ERDALECE/ZeyBack/Pictures/res3.jpg

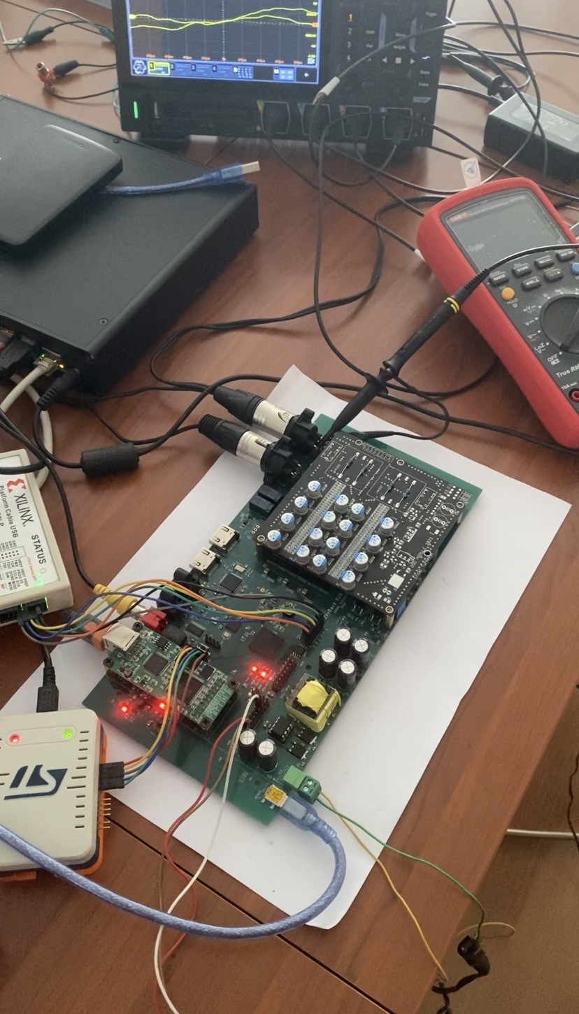
Pictures/res3.jpg
