ERDALECE/ZeyBack/Pictures/res7.jpg

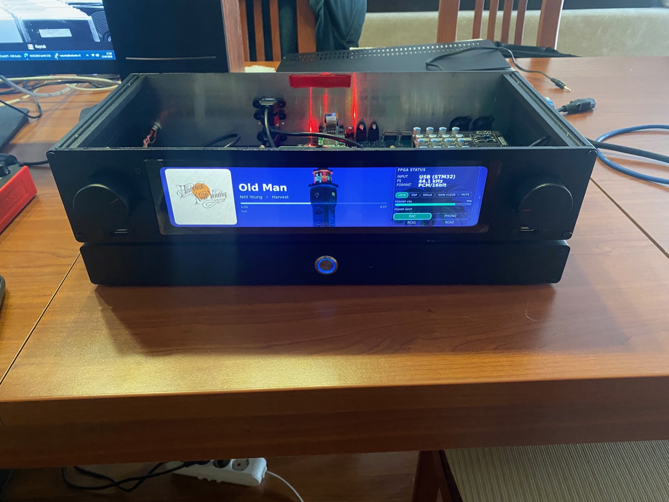
Pictures/res7.jpg
