ERDALECE/ZeyBack/Firmware/Stm32/Core/Inc/192khz.h

#ifndef _192KHZ_BIN_H
#define _192KHZ_BIN_H

static const unsigned char _192khz_bin[] = {
		0x00, 0xff, 0xff, 0xff, 0xff, 0xff, 0xff, 0x00, 0x05, 0xd7, 0x00, 0x00,
		0x00, 0x00, 0x00, 0x00, 0xff, 0x23, 0x01, 0x03, 0x80, 0x32, 0x1f, 0x78,
		0x07, 0xee, 0x95, 0xa3, 0x54, 0x4c, 0x99, 0x26, 0x0f, 0x50, 0x54, 0x00,
		0x00, 0x00, 0x01, 0x01, 0x01, 0x01, 0x01, 0x01, 0x01, 0x01, 0x01, 0x01,
		0x01, 0x01, 0x01, 0x01, 0x01, 0x01, 0x29, 0x36, 0x80, 0xa0, 0x70, 0x38,
		0x1f, 0x40, 0x30, 0x20, 0x35, 0x00, 0x63, 0xc8, 0x10, 0x00, 0x00, 0x1a,
		0x00, 0x00, 0x00, 0xfd, 0x00, 0x17, 0xf0, 0x0f, 0xff, 0x0e, 0x00, 0x0a,
		0x20, 0x20, 0x20, 0x20, 0x20, 0x20, 0x00, 0x00, 0x00, 0xfc, 0x00, 0x31,
		0x39, 0x32, 0x30, 0x78, 0x31, 0x30, 0x38, 0x30, 0x20, 0x43, 0x56, 0x54,
		0x00, 0x00, 0x00, 0x00, 0x00, 0x00, 0x00, 0x00, 0x00, 0x00, 0x00, 0x00,
		0x00, 0x00, 0x00, 0x00, 0x00, 0x00, 0x01, 0x0b, 0x02, 0x03, 0x18, 0x40,
		0x23, 0x09, 0x7e, 0x07, 0x67, 0x03, 0x0c, 0x00, 0x00, 0x00, 0x10, 0x1c,
		0x67, 0xd8, 0x5d, 0xc4, 0x01, 0x1c, 0x80, 0x00, 0x00, 0x00, 0x00, 0x00,
		0x00, 0x00, 0x00, 0x00, 0x00, 0x00, 0x00, 0x00, 0x00, 0x00, 0x00, 0x00,
		0x00, 0x00, 0x00, 0x00, 0x00, 0x00, 0x00, 0x00, 0x00, 0x00, 0x00, 0x00,
		0x00, 0x00, 0x00, 0x00, 0x00, 0x00, 0x00, 0x00, 0x00, 0x00, 0x00, 0x00,
		0x00, 0x00, 0x00, 0x00, 0x00, 0x00, 0x00, 0x00, 0x00, 0x00, 0x00, 0x00,
		0x00, 0x00, 0x00, 0x00, 0x00, 0x00, 0x00, 0x00, 0x00, 0x00, 0x00, 0x00,
		0x00, 0x00, 0x00, 0x00, 0x00, 0x00, 0x00, 0x00, 0x00, 0x00, 0x00, 0x00,
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

  // Filler / reserved (till byte 255)
  0x00, 0x00, 0x00, 0x00, 0x00, 0x00,
  0x00, 0x00, 0x00, 0x00, 0x00, 0x00,
  0x00, 0x00, 0x00, 0x00,

  // Checksum Block 1 (Byte 255)
  0xF9  // <-- Checksum byte for 2nd block: makes total sum % 256 == 0
};

unsigned char EDID_Buf[2][256] ;

/*
uint8_t TX_ADV7611_EDID0 [2] = {0x00, 0x00};
uint8_t TX_ADV7611_EDID1 [2] = {0x01, 0xff};
uint8_t TX_ADV7611_EDID2 [2] = {0x02, 0xff};
uint8_t TX_ADV7611_EDID3 [2] = {0x03, 0xff};
uint8_t TX_ADV7611_EDID4 [2] = {0x04, 0xff};
uint8_t TX_ADV7611_EDID5 [2] = {0x05, 0xff};
uint8_t TX_ADV7611_EDID6 [2] = {0x06, 0xff};
uint8_t TX_ADV7611_EDID7 [2] = {0x07, 0xff};
uint8_t TX_ADV7611_EDID8 [2] = {0x08, 0x00};
uint8_t TX_ADV7611_EDID9 [2] = {0x09, 0x05};
uint8_t TX_ADV7611_EDID10 [2] = {0x0A, 0xd7};
uint8_t TX_ADV7611_EDID11 [2] = {0x0B, 0x00};
uint8_t TX_ADV7611_EDID12 [2] = {0x0C, 0x00};
uint8_t TX_ADV7611_EDID13 [2] = {0x0D, 0x00};
uint8_t TX_ADV7611_EDID14 [2] = {0x0E, 0x00};
uint8_t TX_ADV7611_EDID15 [2] = {0x0F, 0x00};
uint8_t TX_ADV7611_EDID0 [2] = {0x10, 0xff};
uint8_t TX_ADV7611_EDID1 [2] = {0x11, 0x23};
uint8_t TX_ADV7611_EDID2 [2] = {0x12, 0x01};
uint8_t TX_ADV7611_EDID3 [2] = {0x13, 0x03};
uint8_t TX_ADV7611_EDID4 [2] = {0x44, 0x80};
uint8_t TX_ADV7611_EDID5 [2] = {0x15, 0x32};
uint8_t TX_ADV7611_EDID6 [2] = {0x16, 0x1f};
uint8_t TX_ADV7611_EDID7 [2] = {0x17, 0x78};
uint8_t TX_ADV7611_EDID8 [2] = {0x18, 0x07};
uint8_t TX_ADV7611_EDID9 [2] = {0x19, 0xee};
uint8_t TX_ADV7611_EDID10 [2] = {0x1A, 0x95};
uint8_t TX_ADV7611_EDID11 [2] = {0x1B, 0xa3};
uint8_t TX_ADV7611_EDID12 [2] = {0x1C, 0x54};
uint8_t TX_ADV7611_EDID13 [2] = {0x1D, 0x4c};
uint8_t TX_ADV7611_EDID14 [2] = {0x1E, 0x99};
uint8_t TX_ADV7611_EDID15 [2] = {0x1F, 0x26};
uint8_t TX_ADV7611_EDID0 [2] = {0x20, 0x0f};
uint8_t TX_ADV7611_EDID1 [2] = {0x21, 0x00};
uint8_t TX_ADV7611_EDID2 [2] = {0x22, 0x00};
uint8_t TX_ADV7611_EDID3 [2] = {0x23, 0x00};
uint8_t TX_ADV7611_EDID4 [2] = {0x24, 0x00};
uint8_t TX_ADV7611_EDID5 [2] = {0x25, 0x00};
uint8_t TX_ADV7611_EDID6 [2] = {0x26, 0x00};
uint8_t TX_ADV7611_EDID7 [2] = {0x27, 0x00};
uint8_t TX_ADV7611_EDID8 [2] = {0x28, 0x00};
uint8_t TX_ADV7611_EDID9 [2] = {0x29, 0x00};
uint8_t TX_ADV7611_EDID10 [2] = {0x2A, 0x00};
uint8_t TX_ADV7611_EDID11 [2] = {0x2B, 0x00};
uint8_t TX_ADV7611_EDID12 [2] = {0x2C, 0x00};
uint8_t TX_ADV7611_EDID13 [2] = {0x2D, 0x00};
uint8_t TX_ADV7611_EDID14 [2] = {0x2E, 0x00};
uint8_t TX_ADV7611_EDID15 [2] = {0x2F, 0x00};
*/

#endif /* _192KHZ_BIN_H */
