ERDALECE/ZeyBack/Firmware/Stm32/Core/Inc/SI5340_conf.h

/*
 * SI5340_conf.h
 *
 *  Created on: Jun 30, 2025
 *      Author: Erdalpc
 */

#ifndef INC_SI5340_CONF_H_
#define INC_SI5340_CONF_H_

/*
 * Si5340 Rev D Configuration Register Export Header File
 *
 * This file represents a series of Skyworks Si5340 Rev D
 * register writes that can be performed to load a single configuration
 * on a device. It was created by a Skyworks ClockBuilder Pro
 * export tool.
 *
 * Part:		                                       Si5340 Rev D
 * Design ID:                                          r2rdac
 * Includes Pre/Post Download Control Register Writes: Yes
 * Created By:                                         ClockBuilder Pro v4.15.0.2 [2025-05-07]
 * Timestamp:                                          2025-06-30 00:35:52 GMT+03:00
 *
 * A complete design report corresponding to this export is included at the end
 * of this header file.
 *
 */

si5340_revd_register_t const si5340_revd_registers_98_90[SI5340_REVD_REG_CONFIG_NUM_REGS] =
{

	/* Start configuration preamble */
	{ 0x0B24, 0xC0 },
	{ 0x0B25, 0x00 },
	/* Rev D stuck divider fix */
	{ 0x0502, 0x01 },
	{ 0x0505, 0x03 },
	{ 0x0957, 0x17 },
	{ 0x0B4E, 0x1A },
	/* End configuration preamble */

	/* Delay 300 msec */
	/*    Delay is worst case time for device to complete any calibration */
	/*    that is running due to device state change previous to this script */
	/*    being processed. */

	/* Start configuration registers */
	{ 0x0006, 0x00 },
	{ 0x0007, 0x00 },
	{ 0x0008, 0x00 },
	{ 0x000B, 0x74 },
	{ 0x0017, 0xD0 },
	{ 0x0018, 0xFE },
	{ 0x0021, 0x0F },
	{ 0x0022, 0x00 },
	{ 0x002B, 0x02 },
	{ 0x002C, 0x21 },
	{ 0x002D, 0x00 },
	{ 0x002E, 0x91 },
	{ 0x002F, 0x00 },
	{ 0x0030, 0x00 },
	{ 0x0031, 0x00 },
	{ 0x0032, 0x00 },
	{ 0x0033, 0x00 },
	{ 0x0034, 0x00 },
	{ 0x0035, 0x00 },
	{ 0x0036, 0x91 },
	{ 0x0037, 0x00 },
	{ 0x0038, 0x00 },
	{ 0x0039, 0x00 },
	{ 0x003A, 0x00 },
	{ 0x003B, 0x00 },
	{ 0x003C, 0x00 },
	{ 0x003D, 0x00 },
	{ 0x0041, 0x05 },
	{ 0x0042, 0x00 },
	{ 0x0043, 0x00 },
	{ 0x0044, 0x00 },
	{ 0x009E, 0x00 },
	{ 0x0102, 0x01 },
	{ 0x0112, 0x06 },
	{ 0x0113, 0xCC },
	{ 0x0114, 0x00 },
	{ 0x0115, 0x08 },
	{ 0x0117, 0x01 },
	{ 0x0118, 0x09 },
	{ 0x0119, 0x3B },
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
	/* End configuration registers */

	/* Start configuration postamble */
	{ 0x001C, 0x01 },
	{ 0x0B24, 0xC3 },
	{ 0x0B25, 0x02 },
	/* End configuration postamble */

};





si5340_revd_register_t const si5340_revd_registers_90[SI5340_REVD_REG_CONFIG_NUM_REGS] =
{

	/* Start configuration preamble */
	{ 0x0B24, 0xC0 },
	{ 0x0B25, 0x00 },
	/* Rev D stuck divider fix */
	{ 0x0502, 0x01 },
	{ 0x0505, 0x03 },
	{ 0x0957, 0x17 },
	{ 0x0B4E, 0x1A },
	/* End configuration preamble */

	/* Delay 300 msec */
	/*    Delay is worst case time for device to complete any calibration */
	/*    that is running due to device state change previous to this script */
	/*    being processed. */

	/* Start configuration registers */
	{ 0x0006, 0x00 },
	{ 0x0007, 0x00 },
	{ 0x0008, 0x00 },
	{ 0x000B, 0x74 },
	{ 0x0017, 0xD0 },
	{ 0x0018, 0xFE },
	{ 0x0021, 0x0F },
	{ 0x0022, 0x00 },
	{ 0x002B, 0x02 },
	{ 0x002C, 0x21 },
	{ 0x002D, 0x00 },
	{ 0x002E, 0x89 },
	{ 0x002F, 0x00 },
	{ 0x0030, 0x00 },
	{ 0x0031, 0x00 },
	{ 0x0032, 0x00 },
	{ 0x0033, 0x00 },
	{ 0x0034, 0x00 },
	{ 0x0035, 0x00 },
	{ 0x0036, 0x89 },
	{ 0x0037, 0x00 },
	{ 0x0038, 0x00 },
	{ 0x0039, 0x00 },
	{ 0x003A, 0x00 },
	{ 0x003B, 0x00 },
	{ 0x003C, 0x00 },
	{ 0x003D, 0x00 },
	{ 0x0041, 0x05 },
	{ 0x0042, 0x00 },
	{ 0x0043, 0x00 },
	{ 0x0044, 0x00 },
	{ 0x009E, 0x00 },
	{ 0x0102, 0x01 },
	{ 0x0112, 0x02 },
	{ 0x0113, 0xCC },
	{ 0x0114, 0x00 },
	{ 0x0115, 0x09 },
	{ 0x0117, 0x01 },
	{ 0x0118, 0x09 },
	{ 0x0119, 0x3B },
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
	/* End configuration registers */

	/* Start configuration postamble */
	{ 0x001C, 0x01 },
	{ 0x0B24, 0xC3 },
	{ 0x0B25, 0x02 },
	/* End configuration postamble */

};


si5340_revd_register_t const si5340_revd_registers_11[SI5340_REVD_REG_CONFIG_NUM_REGS] =
{

	/* Start configuration preamble */
	{ 0x0B24, 0xC0 },
	{ 0x0B25, 0x00 },
	/* Rev D stuck divider fix */
	{ 0x0502, 0x01 },
	{ 0x0505, 0x03 },
	{ 0x0957, 0x17 },
	{ 0x0B4E, 0x1A },
	/* End configuration preamble */

	/* Delay 300 msec */
	/*    Delay is worst case time for device to complete any calibration */
	/*    that is running due to device state change previous to this script */
	/*    being processed. */

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
	{ 0x0113, 0xCC },
	{ 0x0114, 0x00 },
	{ 0x0115, 0x09 },
	{ 0x0117, 0x01 },
	{ 0x0118, 0x09 },
	{ 0x0119, 0x3B },
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
	/* End configuration registers */

	/* Start configuration postamble */
	{ 0x001C, 0x01 },
	{ 0x0B24, 0xC3 },
	{ 0x0B25, 0x02 },
	/* End configuration postamble */

};


/*
 * Si5340 Rev D Configuration Register Export Header File
 *
 * This file represents a series of Skyworks Si5340 Rev D
 * register writes that can be performed to load a single configuration
 * on a device. It was created by a Skyworks ClockBuilder Pro
 * export tool.
 *
 * Part:		                                       Si5340 Rev D
 * Design ID:                                          r2rdac
 * Includes Pre/Post Download Control Register Writes: Yes
 * Created By:                                         ClockBuilder Pro v4.15.0.2 [2025-05-07]
 * Timestamp:                                          2025-07-14 20:52:29 GMT+03:00
 *
 * A complete design report corresponding to this export is included at the end
 * of this header file.
 *
 */


si5340_revd_register_t const si5340_revd_registers44[SI5340_REVD_REG_CONFIG_NUM_REGS] =
{

	/* Start configuration preamble */
	{ 0x0B24, 0xC0 },
	{ 0x0B25, 0x00 },
	/* Rev D stuck divider fix */
	{ 0x0502, 0x01 },
	{ 0x0505, 0x03 },
	{ 0x0957, 0x17 },
	{ 0x0B4E, 0x1A },
	/* End configuration preamble */

	/* Delay 300 msec */
	/*    Delay is worst case time for device to complete any calibration */
	/*    that is running due to device state change previous to this script */
	/*    being processed. */

	/* Start configuration registers */
	{ 0x0006, 0x00 },
	{ 0x0007, 0x00 },
	{ 0x0008, 0x00 },
	{ 0x000B, 0x74 },
	{ 0x0017, 0xD0 },
	{ 0x0018, 0xFE },
	{ 0x0021, 0x09 },
	{ 0x0022, 0x00 },
	{ 0x002B, 0x02 },
	{ 0x002C, 0x31 },
	{ 0x002D, 0x01 },
	{ 0x002E, 0x88 },
	{ 0x002F, 0x00 },
	{ 0x0030, 0x00 },
	{ 0x0031, 0x00 },
	{ 0x0032, 0x00 },
	{ 0x0033, 0x00 },
	{ 0x0034, 0x00 },
	{ 0x0035, 0x00 },
	{ 0x0036, 0x88 },
	{ 0x0037, 0x00 },
	{ 0x0038, 0x00 },
	{ 0x0039, 0x00 },
	{ 0x003A, 0x00 },
	{ 0x003B, 0x00 },
	{ 0x003C, 0x00 },
	{ 0x003D, 0x00 },
	{ 0x0041, 0x05 },
	{ 0x0042, 0x00 },
	{ 0x0043, 0x00 },
	{ 0x0044, 0x00 },
	{ 0x009E, 0x00 },
	{ 0x0102, 0x01 },
	{ 0x0112, 0x06 },
	{ 0x0113, 0x09 },
	{ 0x0114, 0x33 },
	{ 0x0115, 0x08 },
	{ 0x0117, 0x01 },
	{ 0x0118, 0x09 },
	{ 0x0119, 0x3B },
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
	/* End configuration registers */

	/* Start configuration postamble */
	{ 0x001C, 0x01 },
	{ 0x0B24, 0xC3 },
	{ 0x0B25, 0x02 },
	/* End configuration postamble */

};


si5340_revd_register_t const si5340_revd_registers48[SI5340_REVD_REG_CONFIG_NUM_REGS] =
{

	/* Start configuration preamble */
	{ 0x0B24, 0xC0 },
	{ 0x0B25, 0x00 },
	/* Rev D stuck divider fix */
	{ 0x0502, 0x01 },
	{ 0x0505, 0x03 },
	{ 0x0957, 0x17 },
	{ 0x0B4E, 0x1A },
	/* End configuration preamble */

	/* Delay 300 msec */
	/*    Delay is worst case time for device to complete any calibration */
	/*    that is running due to device state change previous to this script */
	/*    being processed. */

	/* Start configuration registers */
	{ 0x0006, 0x00 },
	{ 0x0007, 0x00 },
	{ 0x0008, 0x00 },
	{ 0x000B, 0x74 },
	{ 0x0017, 0xD0 },
	{ 0x0018, 0xFE },
	{ 0x0021, 0x09 },
	{ 0x0022, 0x00 },
	{ 0x002B, 0x02 },
	{ 0x002C, 0x31 },
	{ 0x002D, 0x01 },
	{ 0x002E, 0x88 },
	{ 0x002F, 0x00 },
	{ 0x0030, 0x00 },
	{ 0x0031, 0x00 },
	{ 0x0032, 0x00 },
	{ 0x0033, 0x00 },
	{ 0x0034, 0x00 },
	{ 0x0035, 0x00 },
	{ 0x0036, 0x88 },
	{ 0x0037, 0x00 },
	{ 0x0038, 0x00 },
	{ 0x0039, 0x00 },
	{ 0x003A, 0x00 },
	{ 0x003B, 0x00 },
	{ 0x003C, 0x00 },
	{ 0x003D, 0x00 },
	{ 0x0041, 0x05 },
	{ 0x0042, 0x00 },
	{ 0x0043, 0x00 },
	{ 0x0044, 0x00 },
	{ 0x009E, 0x00 },
	{ 0x0102, 0x01 },
	{ 0x0112, 0x06 },
	{ 0x0113, 0xCC },
	{ 0x0114, 0x00 },
	{ 0x0115, 0x08 },
	{ 0x0117, 0x01 },
	{ 0x0118, 0x09 },
	{ 0x0119, 0x3B },
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
	/* End configuration registers */

	/* Start configuration postamble */
	{ 0x001C, 0x01 },
	{ 0x0B24, 0xC3 },
	{ 0x0B25, 0x02 },
	/* End configuration postamble */

};

/*
 * Design Report
 *
 * Overview
 * ========
 *
 * Part:               Si5340ABCD Rev D
 * Design ID:          r2rdac
 * Created By:         ClockBuilder Pro v4.15.0.2 [2025-05-07]
 * Timestamp:          2025-06-30 00:35:51 GMT+03:00
 *
 * Design Rule Check
 * =================
 *
 * Errors:
 * - No errors
 *
 * Warnings:
 * - No warnings
 *
 * Notes:
 * - You have selected CMOS output. Please review AN862 "Optimizing Jitter
 *   Performance in Next Generation Internet Infrastructure Systems" to ensure
 *   your configuration meets your jitter requirements
 *
 * Device Grade
 * ============
 * Maximum Output Frequency: 24.576 MHz
 * Frequency Synthesis Mode: Integer
 * Frequency Plan Grade:     D
 * Minimum Base OPN:         Si5340D*
 *
 * Base       Output Clock         Supported Frequency Synthesis Modes
 * OPN Grade  Frequency Range      (Typical Jitter)
 * ---------  -------------------  --------------------------------------------
 * Si5340A    100 Hz to 1.028 GHz  Integer (< 100 fs) and fractional (< 150 fs)
 * Si5340B    100 Hz to 350 MHz    "
 * Si5340C    100 Hz to 1.028 GHz  Integer only (< 100 fs)
 * Si5340D*   100 Hz to 350 MHz    "
 *
 * * Based on your calculated frequency plan, a Si5340D grade device is
 * sufficient for your design. For more in-system configuration flexibility
 * (higher frequencies and/or to enable fractional synthesis), consider
 * selecting device grade Si5340A when specifying an ordering part number (OPN)
 * for your application. See the datasheet Ordering Guide for more information.
 *
 * Design
 * ======
 * Host Interface:
 *    I/O Power Supply: VDDA (3.3V)
 *    SPI Mode: 4-Wire
 *    I2C Address Range: 116d to 119d / 0x74 to 0x77 (selected via A0/A1 pins)
 *
 * Inputs:
 *    XAXB: Unused
 *     IN0: 50 MHz
 *          Standard
 *     IN1: Unused
 *     IN2: Unused
 *   FB_IN: Unused
 *
 * Outputs:
 *    OUT0: 24.576 MHz
 *          Enabled, LVCMOS In-Phase 3.3 V 22 Ω
 *    OUT1: Unused
 *    OUT2: Unused
 *    OUT3: Unused
 *
 * Frequency Plan
 * ==============
 *
 * Priority: maximize the number of low jitter outputs
 *
 * Fpfd = 50 MHz
 * Fvco = 13.27104 GHz
 * Fms0 = 49.152 MHz
 *
 * P dividers:
 *    P0  = 1
 *    P1  = Unused
 *    P2  = Unused
 *    P3  = Unused
 *    Pxaxb = Unused
 *
 * M = 265.4208
 * N dividers:
 *    N0:
 *       Value: 270
 *       OUT0: 24.576 MHz
 *    N1:
 *       Unused
 *    N2:
 *       Unused
 *    N3:
 *       Unused
 *
 * R dividers:
 *    R0 = 2
 *    R1 = Unused
 *    R2 = Unused
 *    R3 = Unused
 *
 * Dividers listed above show effective values. These values are translated to register settings by ClockBuilder Pro. For the actual register values, see below. Refer to the Family Reference Manual for information on registers related to frequency plan.
 *
 * Digitally Controlled Oscillator (DCO)
 * =====================================
 * Mode: FINC/FDEC
 *
 * N0: DCO Disabled
 *
 * N1: DCO Disabled
 *
 * N2: DCO Disabled
 *
 * N3: DCO Disabled
 *
 * Estimated Power & Junction Temperature
 * ======================================
 * Assumptions:
 *
 * VDD:      1.8 V
 * Ta:       25 °C
 * Theta-JA: 18.30 °C/W (JEDEC Board with 2 m/s airflow)
 *
 *                               Overall  On Chip
 * Condition                     Power    Power    Ta    Tj
 * ----------------------------  -------  -------  ----  ----
 * Typical Ta, Voltage, Current  594 mW   594 mW   25 C  35 C
 *
 *                                    -----------------------
 *                                            Typical
 *                                    -----------------------
 *                                    Voltage  Current  Power
 *        Output  Frequency   Format    (V)     (mA)    (mW)
 *        ------  ----------  ------  -------  -------  -----
 * VDD                                   1.80       96    172
 * VDDA                                  3.30      113    374
 * VDDO0  OUT0    24.576 MHz  LVCMOS (in-phase)     3.30       14     48
 * VDDO1  OUT1        Unused
 * VDDO2  OUT2        Unused
 * VDDO3  OUT3        Unused
 *                                    -------  -------  -----
 *                                       1.80       96    172
 *                                       3.30      128    421
 *                                    -------  -------  -----
 *                                      Total             594
 *                                    -------  -------  -----
 *
 * Note:
 *
 * - Tj is junction temperature. Tj must be less than 125 °C (on Si5340 Revision
 *   D) for device to comply with datasheet specifications. Tj = Ta +
 *   Theta_JA*On_Chip_Power.
 * - Overall power includes on-chip power dissipation and adds differential load
 *   power dissipation to estimate total power requirements.
 * - Above are estimates only: power and temperature should be measured on your
 *   PCB.
 * - Selection of appropriate Theta-JA is required for most accurate estimate.
 *   Ideally, select 'User Specified Theta-JA' and enter a Theta-JA value based
 *   on the thermal properties of your PCB.
 *
 * Settings
 * ========
 *
 * Location      Setting Name         Decimal Value      Hex Value
 * ------------  -------------------  -----------------  -----------------
 * 0x0006[23:0]  TOOL_VERSION         0                  0x000000
 * 0x000B[6:0]   I2C_ADDR             116                0x74
 * 0x0017[0]     SYSINCAL_INTR_MSK    0                  0x0
 * 0x0017[1]     LOSXAXB_INTR_MSK     0                  0x0
 * 0x0017[2]     LOSREF_INTR_MSK      0                  0x0
 * 0x0017[3]     LOL_INTR_MSK         0                  0x0
 * 0x0017[5]     SMB_TMOUT_INTR_MSK   0                  0x0
 * 0x0018[3:0]   LOSIN_INTR_MSK       14                 0xE
 * 0x0021[0]     IN_SEL_REGCTRL       1                  0x1
 * 0x0021[2:1]   IN_SEL               0                  0x0
 * 0x0022[1]     OE                   0                  0x0
 * 0x002B[3]     SPI_3WIRE            0                  0x0
 * 0x002B[5]     AUTO_NDIV_UPDATE     0                  0x0
 * 0x002C[3:0]   LOS_EN               1                  0x1
 * 0x002C[4]     LOSXAXB_DIS          1                  0x1
 * 0x002D[1:0]   LOS0_VAL_TIME        1                  0x1
 * 0x002D[3:2]   LOS1_VAL_TIME        0                  0x0
 * 0x002D[5:4]   LOS2_VAL_TIME        0                  0x0
 * 0x002D[7:6]   LOS3_VAL_TIME        0                  0x0
 * 0x002E[15:0]  LOS0_TRG_THR         136                0x0088
 * 0x0030[15:0]  LOS1_TRG_THR         0                  0x0000
 * 0x0032[15:0]  LOS2_TRG_THR         0                  0x0000
 * 0x0034[15:0]  LOS3_TRG_THR         0                  0x0000
 * 0x0036[15:0]  LOS0_CLR_THR         136                0x0088
 * 0x0038[15:0]  LOS1_CLR_THR         0                  0x0000
 * 0x003A[15:0]  LOS2_CLR_THR         0                  0x0000
 * 0x003C[15:0]  LOS3_CLR_THR         0                  0x0000
 * 0x0041[4:0]   LOS0_DIV_SEL         5                  0x05
 * 0x0042[4:0]   LOS1_DIV_SEL         0                  0x00
 * 0x0043[4:0]   LOS2_DIV_SEL         0                  0x00
 * 0x0044[4:0]   LOS3_DIV_SEL         0                  0x00
 * 0x009E[7:4]   LOL_SET_THR          0                  0x0
 * 0x0102[0]     OUTALL_DISABLE_LOW   1                  0x1
 * 0x0112[0]     OUT0_PDN             0                  0x0
 * 0x0112[1]     OUT0_OE              1                  0x1
 * 0x0112[2]     OUT0_RDIV_FORCE2     1                  0x1
 * 0x0113[2:0]   OUT0_FORMAT          4                  0x4
 * 0x0113[3]     OUT0_SYNC_EN         1                  0x1
 * 0x0113[5:4]   OUT0_DIS_STATE       0                  0x0
 * 0x0113[7:6]   OUT0_CMOS_DRV        3                  0x3
 * 0x0114[3:0]   OUT0_CM              0                  0x0
 * 0x0114[6:4]   OUT0_AMPL            0                  0x0
 * 0x0115[2:0]   OUT0_MUX_SEL         0                  0x0
 * 0x0115[5:4]   OUT0_VDD_SEL         0                  0x0
 * 0x0115[3]     OUT0_VDD_SEL_EN      1                  0x1
 * 0x0115[7:6]   OUT0_INV             0                  0x0
 * 0x0117[0]     OUT1_PDN             1                  0x1
 * 0x0117[1]     OUT1_OE              0                  0x0
 * 0x0117[2]     OUT1_RDIV_FORCE2     0                  0x0
 * 0x0118[2:0]   OUT1_FORMAT          1                  0x1
 * 0x0118[3]     OUT1_SYNC_EN         1                  0x1
 * 0x0118[5:4]   OUT1_DIS_STATE       0                  0x0
 * 0x0118[7:6]   OUT1_CMOS_DRV        0                  0x0
 * 0x0119[3:0]   OUT1_CM              11                 0xB
 * 0x0119[6:4]   OUT1_AMPL            3                  0x3
 * 0x011A[2:0]   OUT1_MUX_SEL         0                  0x0
 * 0x011A[5:4]   OUT1_VDD_SEL         2                  0x2
 * 0x011A[3]     OUT1_VDD_SEL_EN      1                  0x1
 * 0x011A[7:6]   OUT1_INV             0                  0x0
 * 0x0126[0]     OUT2_PDN             1                  0x1
 * 0x0126[1]     OUT2_OE              0                  0x0
 * 0x0126[2]     OUT2_RDIV_FORCE2     0                  0x0
 * 0x0127[2:0]   OUT2_FORMAT          1                  0x1
 * 0x0127[3]     OUT2_SYNC_EN         1                  0x1
 * 0x0127[5:4]   OUT2_DIS_STATE       0                  0x0
 * 0x0127[7:6]   OUT2_CMOS_DRV        0                  0x0
 * 0x0128[3:0]   OUT2_CM              11                 0xB
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
 * 0x0A26[3]     N3_HIGH_FREQ         0                  0x0
 * 0x0B44[3:0]   PDIV_ENB             15                 0xF
 * 0x0B4A[4:0]   N_CLK_DIS            14                 0x0E
 * 0x0B57[11:0]  VCO_RESET_CALCODE    259                0x103
 *
 *
 */

#endif /* INC_SI5340_CONF_H_ */
