ERDALECE/ZeyBack/Firmware/Stm32/Core/Src/IRremote.c

#include "IRremote.h"
#include "main.h"



void IR_TIM3_PeriodElapsedCallback(void)
{
    uint8_t irdata = RECIV_PIN; // пин для приёма

    irparams.timer++;  // One more 50uS tick
    if (irparams.rawlen >= RAWBUF) irparams.rcvstate = STATE_OVERFLOW;  // Buffer overflow

    switch (irparams.rcvstate)
    {
        case STATE_IDLE: // In the middle of a gap
            if (irdata == MARK)
            {
                if (irparams.timer < GAP_TICKS)  // Not big enough to be a gap.
                {
                    irparams.timer = 0;
                }
                else
                {
                    // Gap just ended; Record duration; Start recording transmission
                    irparams.overflow = false;
                    irparams.rawlen  = 0;
                    irparams.rawbuf[irparams.rawlen++] = irparams.timer;
                    irparams.timer = 0;
                    irparams.rcvstate = STATE_MARK;
                }
            }
            break;

        case STATE_MARK:  // Timing Mark
            if (irdata == SPACE) // Mark ended; Record time
            {
                irparams.rawbuf[irparams.rawlen++] = irparams.timer;
                irparams.timer = 0;
                irparams.rcvstate = STATE_SPACE;
            }
            break;

        case STATE_SPACE:  // Timing Space
            if (irdata == MARK) // Space just ended; Record time
            {
                irparams.rawbuf[irparams.rawlen++] = irparams.timer;
                irparams.timer = 0;
                irparams.rcvstate = STATE_MARK;
            }
            else if (irparams.timer > GAP_TICKS) // Space
            {
                irparams.rcvstate = STATE_STOP;
            }
            break;

        case STATE_STOP:  // Waiting; Measuring Gap
            if (irdata == MARK) irparams.timer = 0;  // Reset gap timer
            break;

        case STATE_OVERFLOW:  // Flag up a read overflow; Stop the State Machine
            irparams.overflow = true;
            irparams.rcvstate = STATE_STOP;
            break;
    }
}


////////////////////////////////////////////////////////////////////////////////////////////
int MATCH(int measured, int desired)
{
 	return ((measured >= TICKS_LOW(desired)) && (measured <= TICKS_HIGH(desired)));
}

int MATCH_MARK(int measured_ticks, int desired_us)
{
	return ((measured_ticks >= TICKS_LOW(desired_us + MARK_EXCESS)) && (measured_ticks <= TICKS_HIGH(desired_us + MARK_EXCESS)));
}

int MATCH_SPACE(int measured_ticks, int desired_us)
{
	return ((measured_ticks >= TICKS_LOW(desired_us - MARK_EXCESS)) && (measured_ticks <= TICKS_HIGH(desired_us - MARK_EXCESS)));
}

//////////////////////////////////////////irRecv.c//////////////////////////////////////////////////

int16_t my_decode(decode_results *results)
{
	results->rawbuf = irparams.rawbuf;
	results->rawlen = irparams.rawlen;
	results->overflow = irparams.overflow;

	if(irparams.rcvstate != STATE_STOP) return false;

	#if DECODE_NEC
		if(decodeNEC(results)) return true;
	#endif

	#if DECODE_SONY
		if(decodeSony(results)) return true;
	#endif

	#if DECODE_SANYO
		if(decodeSanyo(results)) return true;
	#endif

	#if DECODE_MITSUBISHI
		if(decodeMitsubishi(results)) return true;
	#endif

	#if DECODE_RC5
		if(decodeRC5(results)) return true;
	#endif

	#if DECODE_RC6
		if(decodeRC6(results)) return true;
	#endif

	#if DECODE_PANASONIC
		if(decodePanasonic(results)) return true;
	#endif

	#if DECODE_LG
		if(decodeLG(results)) return true;
	#endif

	#if DECODE_JVC
		if(decodeJVC(results)) return true;
	#endif

	#if DECODE_SAMSUNG
		if(decodeSAMSUNG(results)) return true;
	#endif

	#if DECODE_WHYNTER
		if(decodeWhynter(results)) return true;
	#endif

	#if DECODE_AIWA_RC_T501
		if(decodeAiwaRCT501(results)) return true;
	#endif

	#if DECODE_DENON
		if(decodeDenon(results)) return true;
	#endif

	if(decodeHash(results)) return true;
	my_resume();
	return false;
}

void my_enableIRIn() // initialization
{
	//DWT_Init(); // старт счётчика микросекунд

	HAL_TIM_Base_DeInit(&htim3);

	TIM_ClockConfigTypeDef sClockSourceConfig = {0};
	TIM_MasterConfigTypeDef sMasterConfig = {0};

	htim3.Instance = TIM3;
	htim3.Init.Prescaler = MYPRESCALER;
	htim3.Init.CounterMode = TIM_COUNTERMODE_UP;
	htim3.Init.Period = MYPERIOD;
	htim3.Init.ClockDivision = TIM_CLOCKDIVISION_DIV1;
	htim3.Init.AutoReloadPreload = TIM_AUTORELOAD_PRELOAD_DISABLE;
	HAL_TIM_Base_Init(&htim3);
	sClockSourceConfig.ClockSource = TIM_CLOCKSOURCE_INTERNAL;
	HAL_TIM_ConfigClockSource(&htim3, &sClockSourceConfig);
	sMasterConfig.MasterOutputTrigger = TIM_TRGO_RESET;
	sMasterConfig.MasterSlaveMode = TIM_MASTERSLAVEMODE_DISABLE;
	HAL_TIMEx_MasterConfigSynchronization(&htim3, &sMasterConfig);

	irparams.rcvstate = STATE_IDLE;
	irparams.rawlen = 0;

	HAL_TIM_Base_Start_IT(&htim3);
}

uint8_t my_isIdle() // Return if receiving new IR signals
{
	return (irparams.rcvstate == STATE_IDLE || irparams.rcvstate == STATE_STOP) ? true : false;
}

void my_resume() // Restart the ISR state machine
{
	irparams.rcvstate = STATE_IDLE;
	irparams.rawlen = 0;
}

int compare(unsigned int oldval, unsigned int newval)
{
	if(newval < oldval * .8) return 0;
	else if(oldval < newval * .8) return 2;
	else return 1;
}

#define FNV_PRIME_32 16777619
#define FNV_BASIS_32 2166136261

int32_t decodeHash(decode_results *results)
{
	int32_t hash = FNV_BASIS_32;

	// Require at least 6 samples to prevent triggering on noise
	if(results->rawlen < 6) return false;

	for(int16_t i = 1; (i + 2) < results->rawlen; i++)
	{
		int16_t value = compare(results->rawbuf[i], results->rawbuf[i+2]);
		hash = (hash * FNV_PRIME_32) ^ value; // Add value into the hash
	}

	results->value = hash;
	results->bits = 32;
	results->decode_type = UNKNOWN;
	return true;
}
