ERDALECE/ZeyBack/Firmware/Stm32/Core/Inc/defines.h

/*
 * defines.h
 *
 *  Created on: Feb 16, 2025
 *      Author: erdal
 */

#ifndef INC_DEFINES_H_
#define INC_DEFINES_H_

#include "stm32h7xx_hal.h"



#define recive_IR_Pin IR_Pin
#define recive_IR_GPIO_Port IR_GPIO_Port




#endif /* INC_DEFINES_H_ */
